JordanAceto/SSI2140_12_stage_phase_shifter/main_pcb/docs/2D/SSI2140_phase_shifter-bottom.jpg

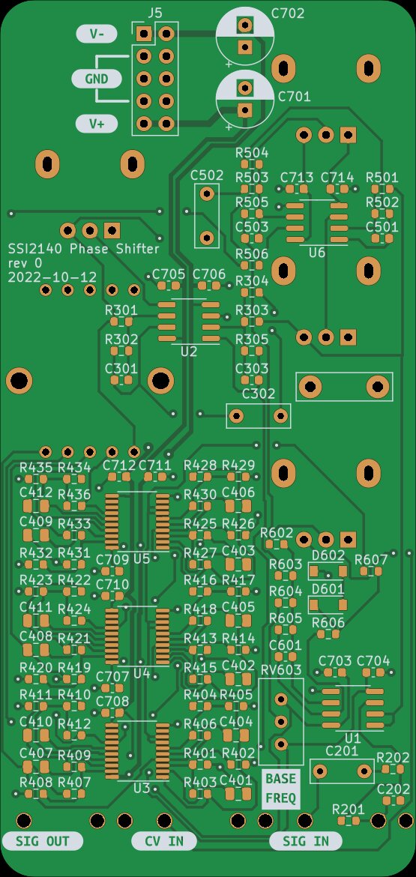
main_pcb/docs/2D/SSI2140_phase_shifter-bottom.jpg
