JordanAceto/SSI2140_12_stage_phase_shifter/main_pcb/docs/html_nav/images/cat_PCB_SSI2140_phase_shifter-F_Cu.png

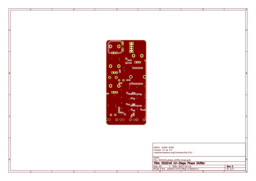
main_pcb/docs/html_nav/images/cat_PCB_SSI2140_phase_shifter-F_Cu.png
