JordanAceto/SSI2140_12_stage_phase_shifter/main_pcb/docs/html_nav/images/cat_pcb_top_jpg_SSI2140_phase_shifter-top.png

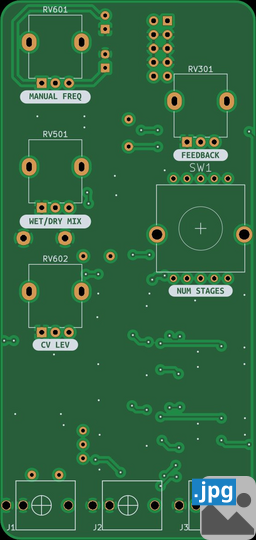
main_pcb/docs/html_nav/images/cat_pcb_top_jpg_SSI2140_phase_shifter-top.png
