JordanAceto/SSI2140_12_stage_phase_shifter/main_pcb/docs/html_nav/images/cat_pdf_pcb_print_BCu_SSI2140_phase_shifter-B_Cu.png

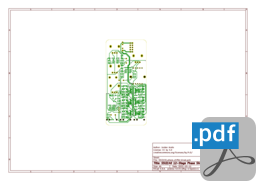
main_pcb/docs/html_nav/images/cat_pdf_pcb_print_BCu_SSI2140_phase_shifter-B_Cu.png
