JordanAceto/SSI2140_12_stage_phase_shifter/main_pcb/docs/html_nav/images/cat_pdf_sch_print_SSI2140_phase_shifter-schematic.png

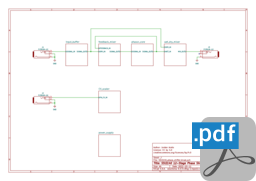
main_pcb/docs/html_nav/images/cat_pdf_sch_print_SSI2140_phase_shifter-schematic.png
