JordanAceto/SSI2140_12_stage_phase_shifter/main_pcb/docs/2D/individual_layers/SSI2140_phase_shifter-F_Silkscreen.pdf

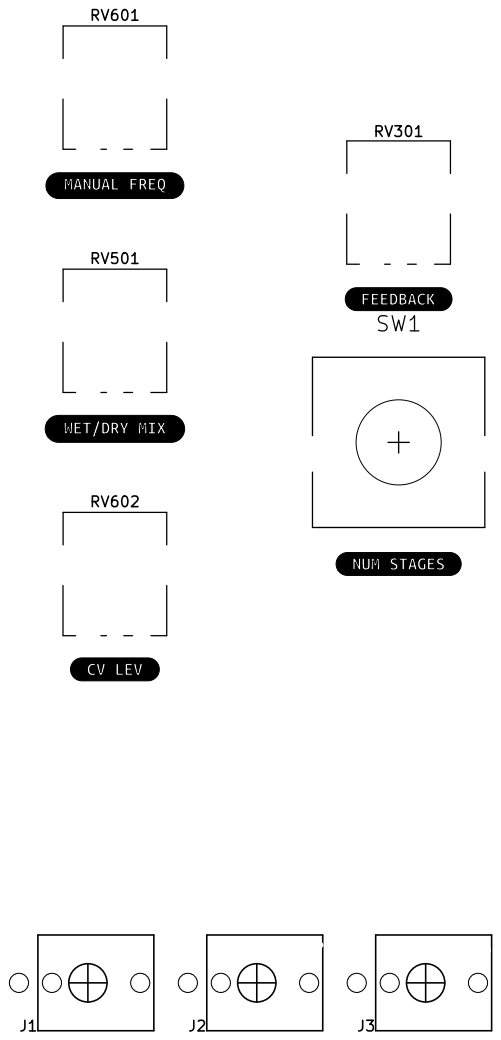
[picture p36: page 1]
